RASBI-CARDNAME/Enhanced_directional_speaker/Circuit Diagram/(DUAL)STM32F103C8T6 Ultrasonic Speaker Circuit.kicad_sch

## KiCad design Circuit Diagram/(DUAL)STM32F103C8T6 Ultrasonic Speaker Circuit.kicad_sch (2025-07-09)

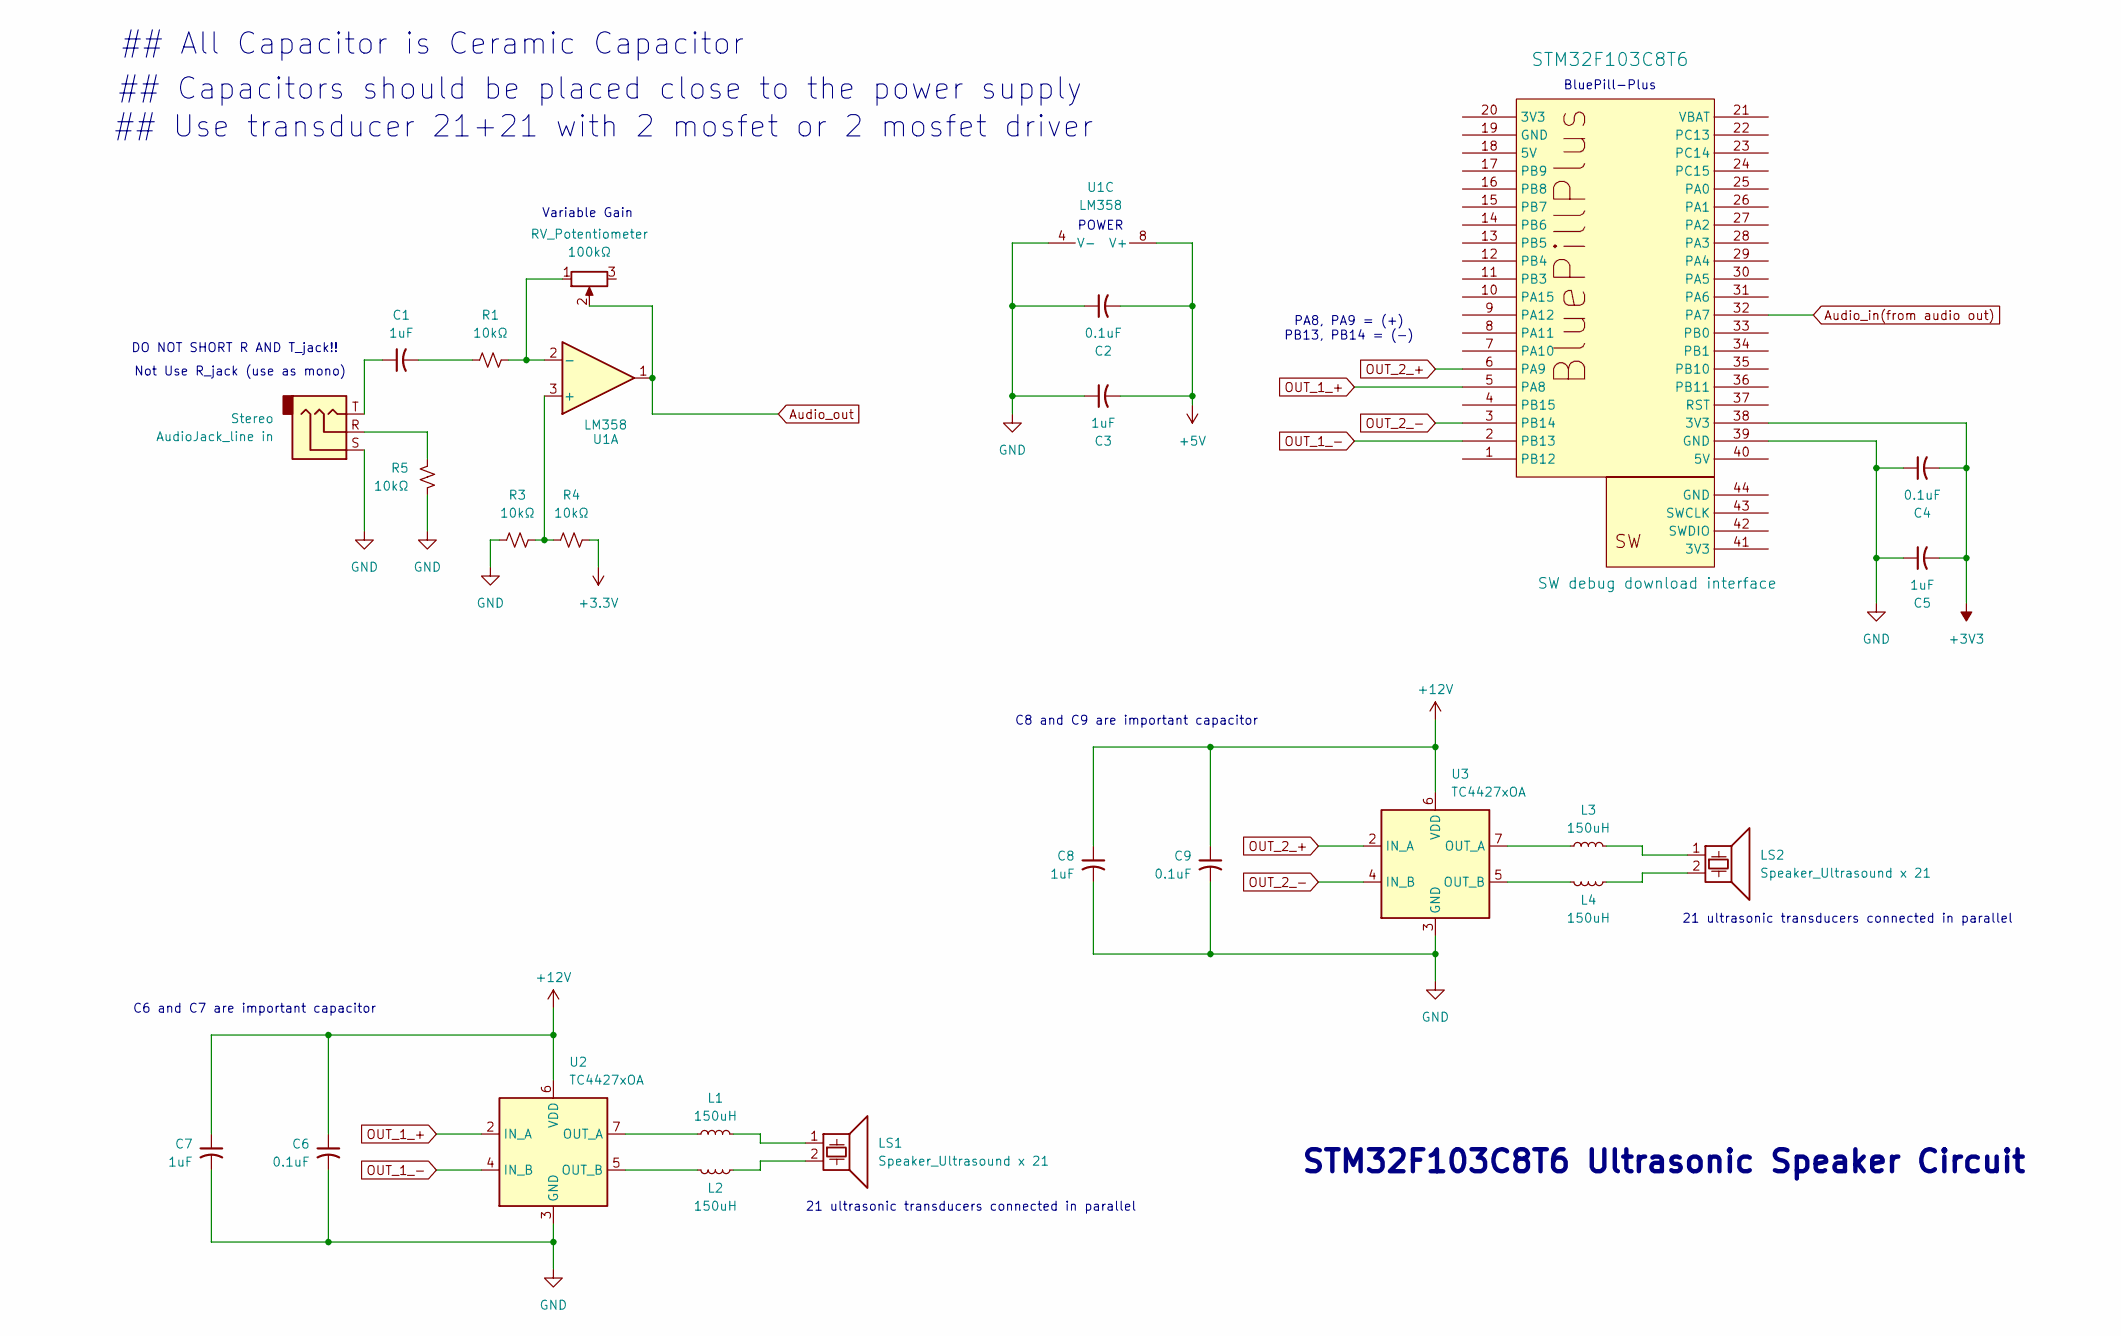
[picture p3: schematic (DUAL)STM32F103C8T6 Ultrasonic Speaker Circuit.kicad_sch]

Parts:
11: SW debug download interface; BluePillPlus
150uH: L2
BluePill-Plus: STM32F103C8T6; BluePillPlus
C1, C3, C5, C7, C8: 1uF
C2, C4, C6, C9: 0.1uF
L1, L3: 150uH
LS1, LS2: Speaker_Ultrasound x 21
R1, R3, R4, R5: 10kΩ
RV_Potentiometer: 100kΩ
Stereo: AudioJack_line in
U1: LM358
U2, U3: TC4427xOA; SOIC-8_3.9x4.9mm_P1.27mm

Connections:
+3.3V: R4.2
+3V3: BluePill-Plus.38 (3V3), C4.2, C5.2
+5V: C2.2, C3.2, U1.8 (V+)
+12V: C6.1, C7.1, C8.1, C9.1, U2.6 (VDD), U3.6 (VDD)
Audio_in(from audio out): BluePill-Plus.32 (PA7)
Audio_out: RV_Potentiometer.2, U1.1
GND: BluePill-Plus.39 (GND), C2.1, C3.1, C4.1, C5.1, C6.2, C7.2, C8.2, C9.2, R3.1, R5.2, Stereo.S, U1.4 (V-), U2.3 (GND), U3.3 (GND)
unnamed: 150uH.1, U2.5 (OUT_B), U3.5 (OUT_B)
unnamed: 150uH.2, LS1.2, LS2.2
unnamed: C1.1, Stereo.T
unnamed: C1.2, R1.1
unnamed: L1.1, U2.7 (OUT_A)
unnamed: L1.2, LS1.1
unnamed: L3.1, U3.7 (OUT_A)
unnamed: L3.2, LS2.1
unnamed: R1.2, RV_Potentiometer.1, U1.2 (-)
unnamed: R3.2, R4.1, U1.3 (+)
unnamed: R5.1, Stereo.R
OUT_1_+: BluePill-Plus.5 (PA8), U2.2 (IN_A)
OUT_1_-: BluePill-Plus.2 (PB13), U2.4 (IN_B)
OUT_2_+: BluePill-Plus.6 (PA9), U3.2 (IN_A)
OUT_2_-: BluePill-Plus.3 (PB14), U3.4 (IN_B)

Notes on the sheet:
DO NOT SHORT R AND T_jack!!
## All Capacitor is Ceramic Capacitor
21 ultrasonic transducers connected in parallel
## Capacitors should be placed close to the power supply
BluePill-Plus
STM32F103C8T6 Ultrasonic Speaker Circuit
## Use transducer 21+21 with 2 mosfet or 2 mosfet driver
Variable Gain
C8 and C9 are important capacitor
C6 and C7 are important capacitor
POWER
Not Use R_jack (use as mono)
PA8, PA9 = (+) PB13, PB14 = (-)
