RASBI-CARDNAME/Enhanced_directional_speaker/Circuit Diagram/speaker_array.kicad_sch

## KiCad design Circuit Diagram/speaker_array.kicad_sch (2025-07-09)

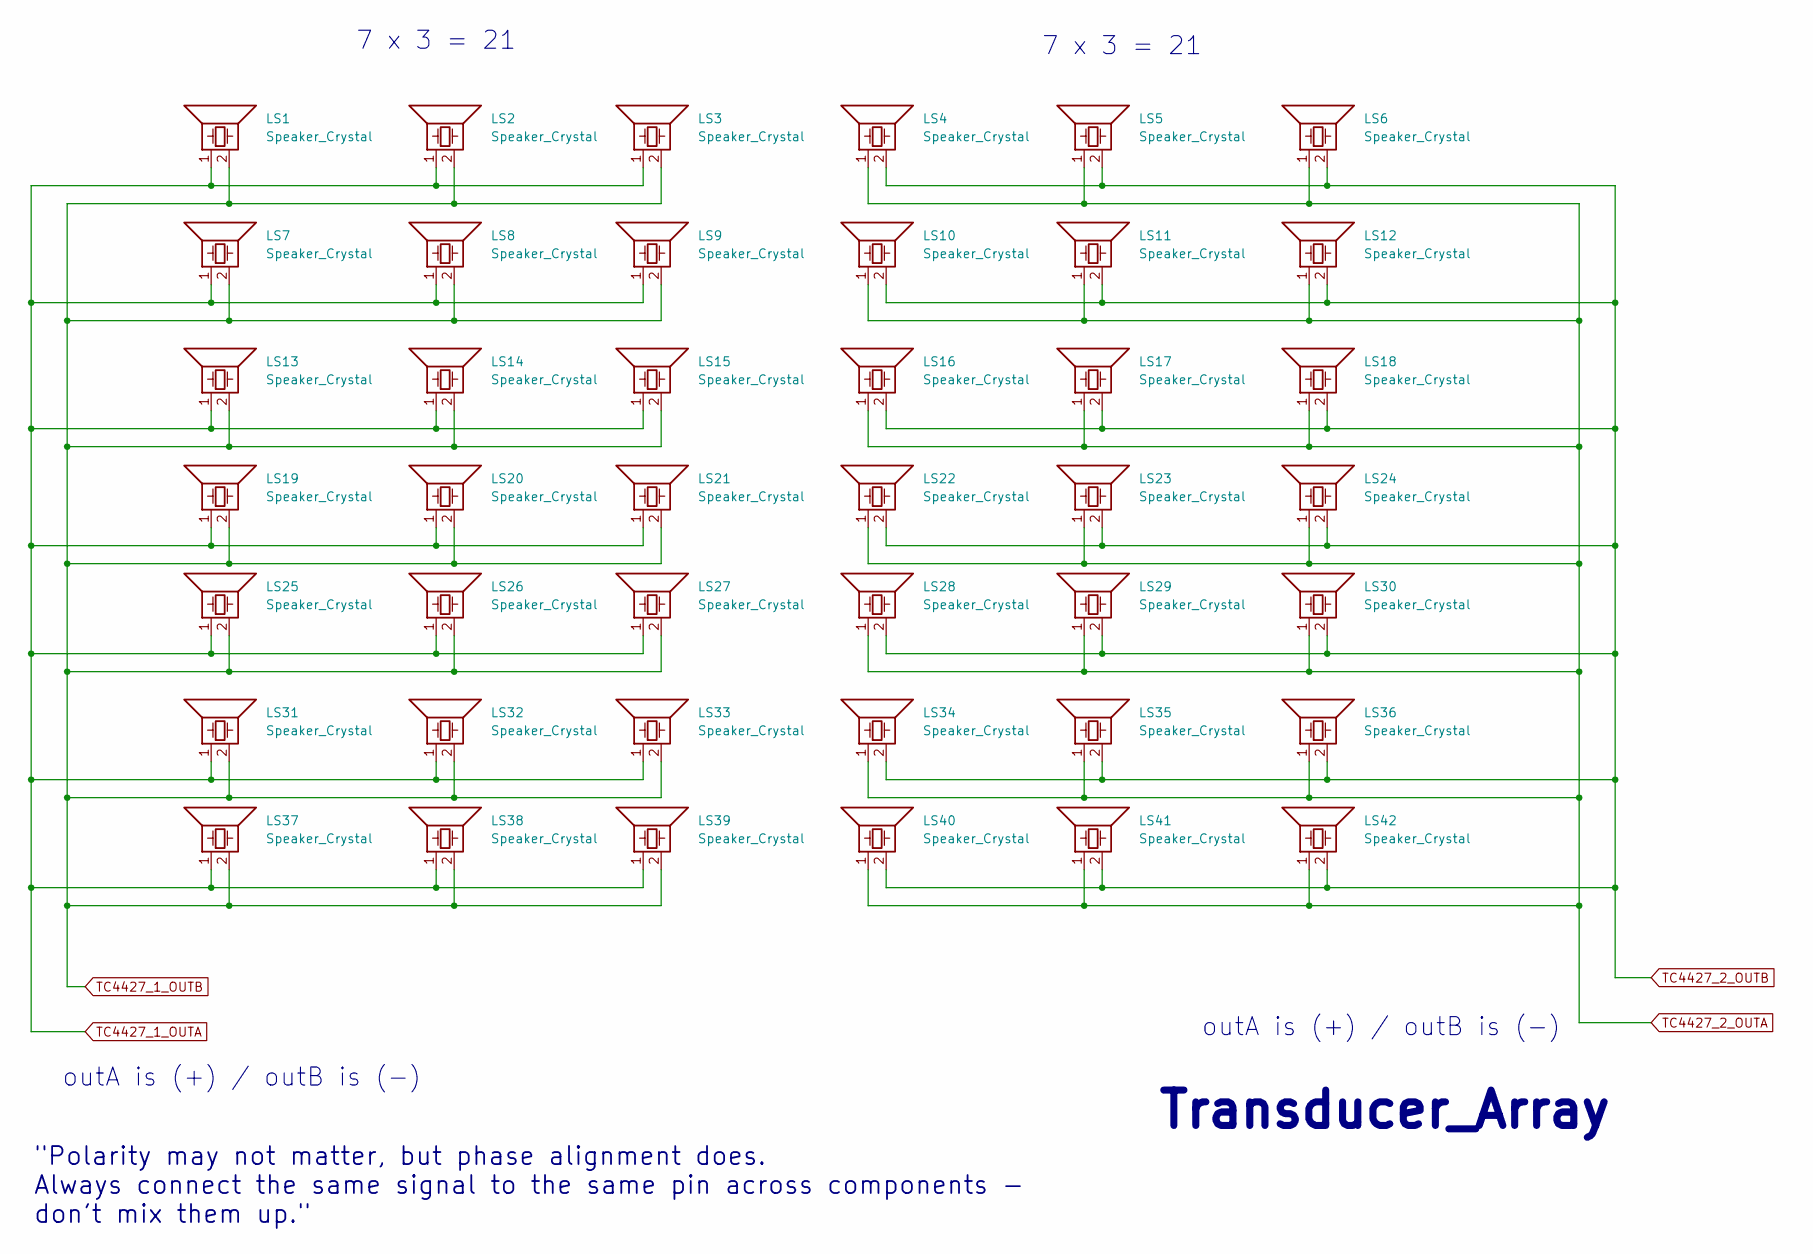
[picture p4: schematic speaker_array.kicad_sch]

Parts:
LS1, LS2, LS3, LS4, LS5, LS6, LS7, LS8, LS9, LS10, LS11, LS12, LS13, LS14, LS15, LS16, LS17, LS18, LS19, LS20, LS21, LS22, LS23, LS24, LS25, LS26, LS27, LS28, LS29, LS30, LS31, LS32, LS33, LS34, LS35, LS36, LS37, LS38, LS39, LS40, LS41, LS42: Speaker_Crystal

Connections:
TC4427_1_OUTA: LS1.1, LS2.1, LS3.1, LS7.1, LS8.1, LS9.1, LS13.1, LS14.1, LS15.1, LS19.1, LS20.1, LS21.1, LS25.1, LS26.1, LS27.1, LS31.1, LS32.1, LS33.1, LS37.1, LS38.1, LS39.1
TC4427_1_OUTB: LS1.2, LS2.2, LS3.2, LS7.2, LS8.2, LS9.2, LS13.2, LS14.2, LS15.2, LS19.2, LS20.2, LS21.2, LS25.2, LS26.2, LS27.2, LS31.2, LS32.2, LS33.2, LS37.2, LS38.2, LS39.2
TC4427_2_OUTA: LS4.1, LS5.1, LS6.1, LS10.1, LS11.1, LS12.1, LS16.1, LS17.1, LS18.1, LS22.1, LS23.1, LS24.1, LS28.1, LS29.1, LS30.1, LS34.1, LS35.1, LS36.1, LS40.1, LS41.1, LS42.1
TC4427_2_OUTB: LS4.2, LS5.2, LS6.2, LS10.2, LS11.2, LS12.2, LS16.2, LS17.2, LS18.2, LS22.2, LS23.2, LS24.2, LS28.2, LS29.2, LS30.2, LS34.2, LS35.2, LS36.2, LS40.2, LS41.2, LS42.2

Notes on the sheet:
Transducer_Array
outA is (+) / outB is (-)
7 x 3 = 21
"Polarity may not matter, but phase alignment does. Always connect the same signal to the same pin across components - don't mix them up."
